Aleck-K/NMEA0183USB-Wifi-bridge/img/2.jpg

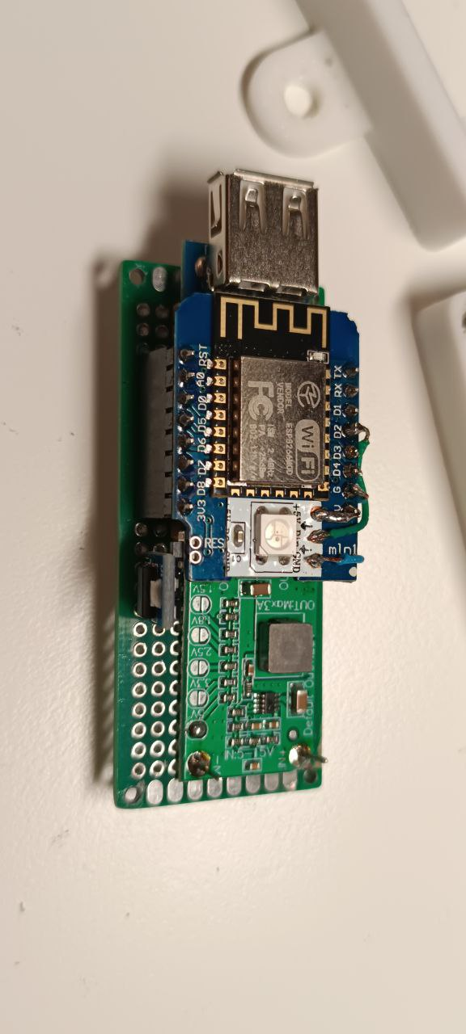
img/2.jpg
