Aleck-K/NMEA0183USB-Wifi-bridge/img/7.jpg

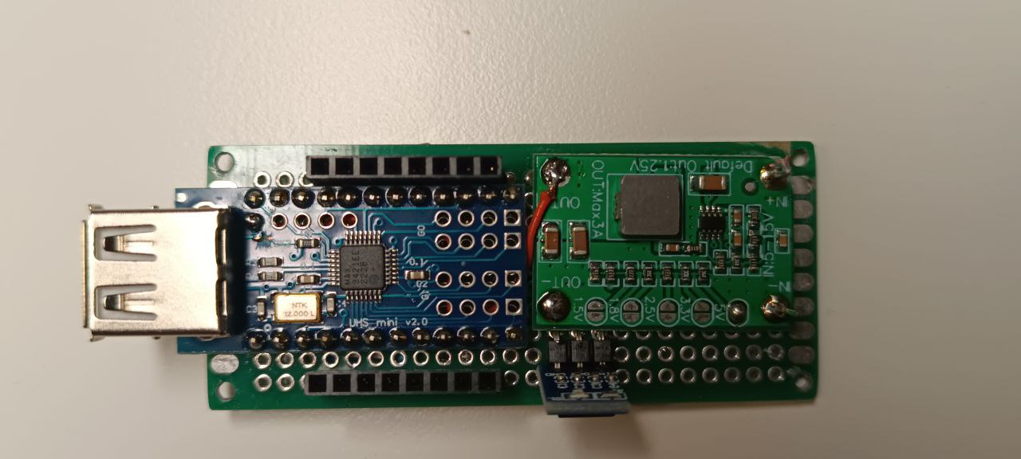
img/7.jpg
